BerandaMegane/Commercial-Power-Measurement-Adapter/CircuitDesign/ver2/sim_ver2.asc

C1: cap; 4.7µ
C2: cap; 200µ
C3: cap; 0.1µ
C4: cap; 0.01µ
D2: diode
D8: zener; BZX84C10VLY
R1: res; 680; pwr=1
R2: res; 250
R3: res; 10k
R4: res; 10k
R5: res; 300k; pwr=1
V1: voltage; SINE(0 141 50 0 0)
V2: voltage; 5
Named nets: 0
.tran 0.2
